maxijra-edu/MUA_UnidadDeteccion/Placa_DetectorParticulas/Componentes/MCP4661T_104E_ML/QFN16_4x4MC_MCH.step

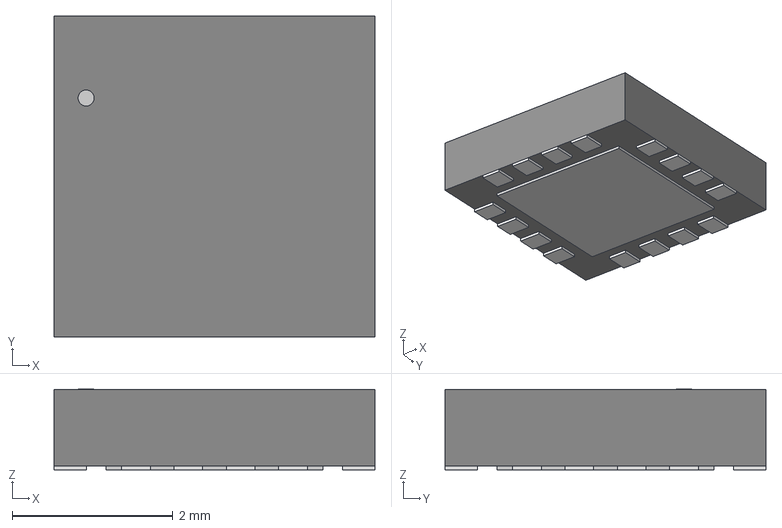
[picture p15: CAD file, 2025-07-07]
Placa_DetectorParticulas/Componentes/MCP4661T_104E_ML/QFN16_4x4MC_MCH.step
3.99 x 3.99 x 1.00 mm
