maxijra-edu/MUA_UnidadDeteccion/Placa_DetectorParticulas/Componentes/MICROFJ-60035-TSV-TR1/MICROFJ-60035-TSV_ONS.step

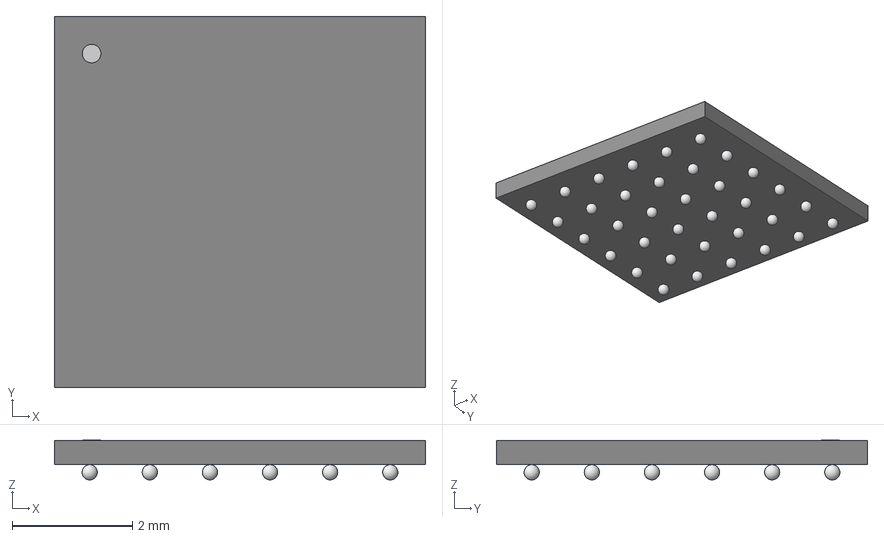
[picture p16: CAD file, 2025-03-27]
Placa_DetectorParticulas/Componentes/MICROFJ-60035-TSV-TR1/MICROFJ-60035-TSV_ONS.step
6.17 x 6.17 x 0.663 mm
