maxijra-edu/MUA_UnidadDeteccion/Placa_DetectorParticulas/Componentes/NXB0108BQ-Q100X/DHVQFN20_SOT764-1_NEX.step

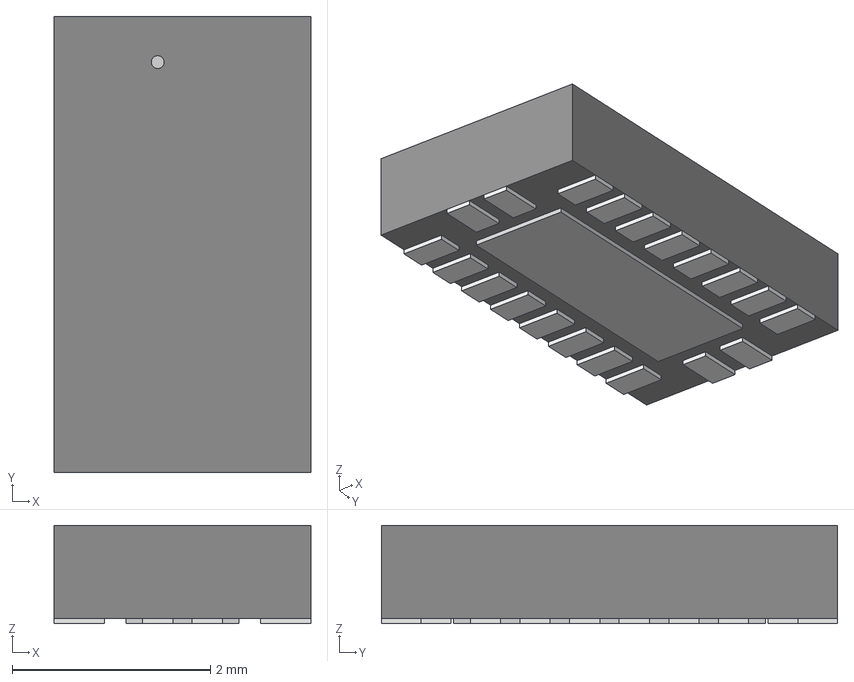
[picture p17: CAD file, 2025-03-27]
Placa_DetectorParticulas/Componentes/NXB0108BQ-Q100X/DHVQFN20_SOT764-1_NEX.step
2.59 x 4.60 x 0.993 mm
