maxijra-edu/MUA_UnidadDeteccion/Placa_DetectorParticulas/Componentes/OPA855QDSGRQ1/DSG0008A.stp

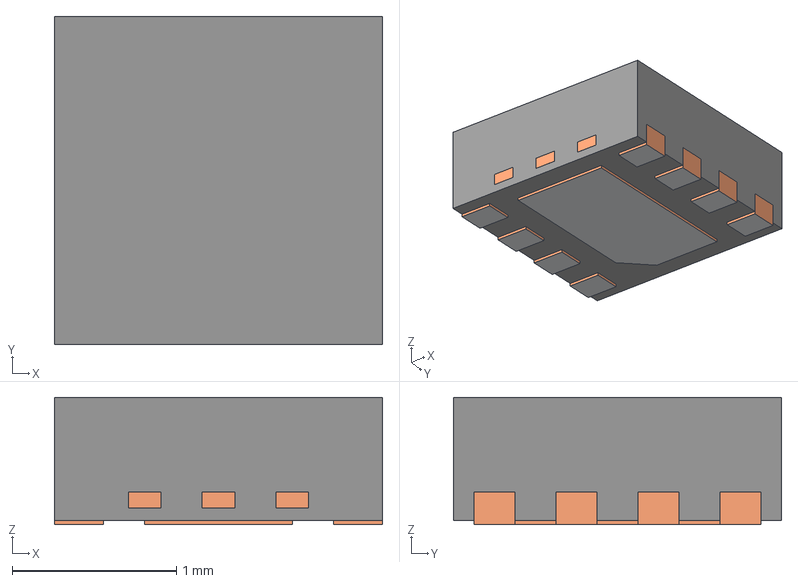
[picture p18: CAD file, 2025-03-27]
Placa_DetectorParticulas/Componentes/OPA855QDSGRQ1/DSG0008A.stp
2.00 x 2.00 x 0.775 mm
BODY-SON
FRAME-DSG0008A
PIN1-ID
