maxijra-edu/MUA_UnidadDeteccion/Placa_DetectorParticulas/Componentes/PCA9306IDCURQ1/DCU0008A.stp

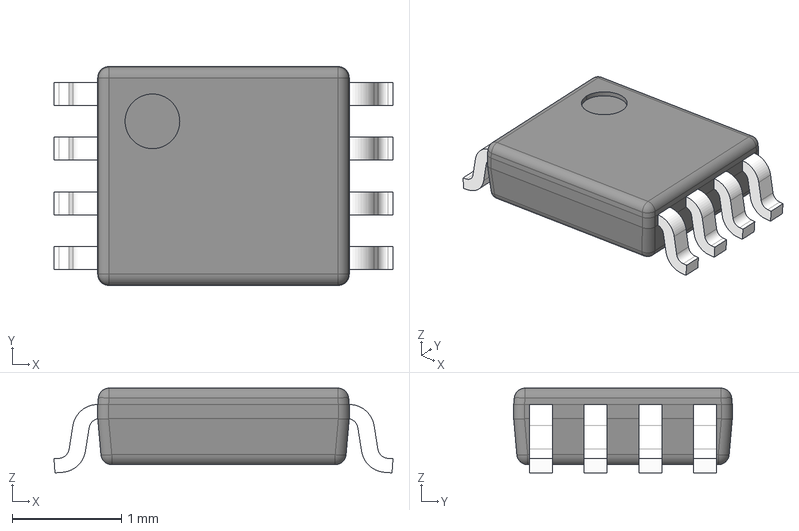
[picture p19: CAD file, 2025-03-27]
Placa_DetectorParticulas/Componentes/PCA9306IDCURQ1/DCU0008A.stp
3.10 x 2.00 x 0.775 mm
BODY-VSSOP
LEAD-VSSOP x 8
