maxijra-edu/MUA_UnidadDeteccion/Placa_DetectorParticulas/Componentes/PMEG4005CEJX/SOD523_NEX.step

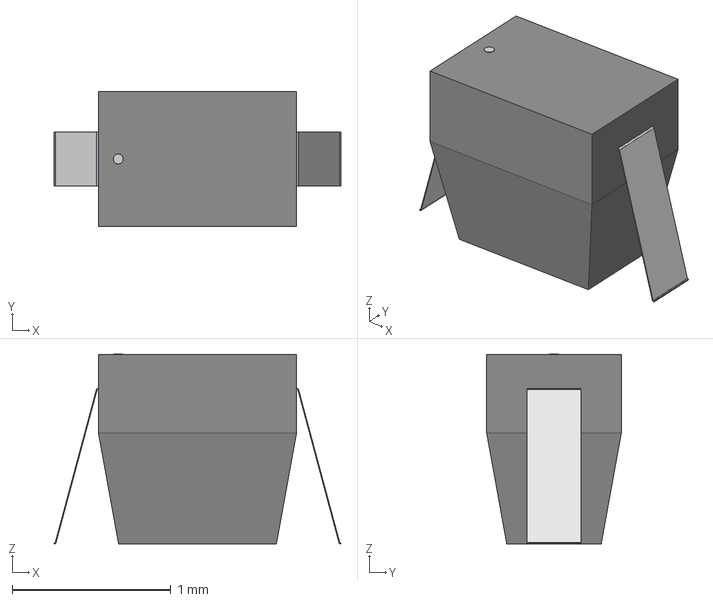
[picture p20: CAD file, 2025-03-27]
Placa_DetectorParticulas/Componentes/PMEG4005CEJX/SOD523_NEX.step
1.81 x 0.85 x 1.20 mm
