maxijra-edu/MUA_UnidadDeteccion/Placa_DetectorParticulas/Componentes/SN74LV1T04QDCKRQ1/SC70-5_DCK_TEX.step

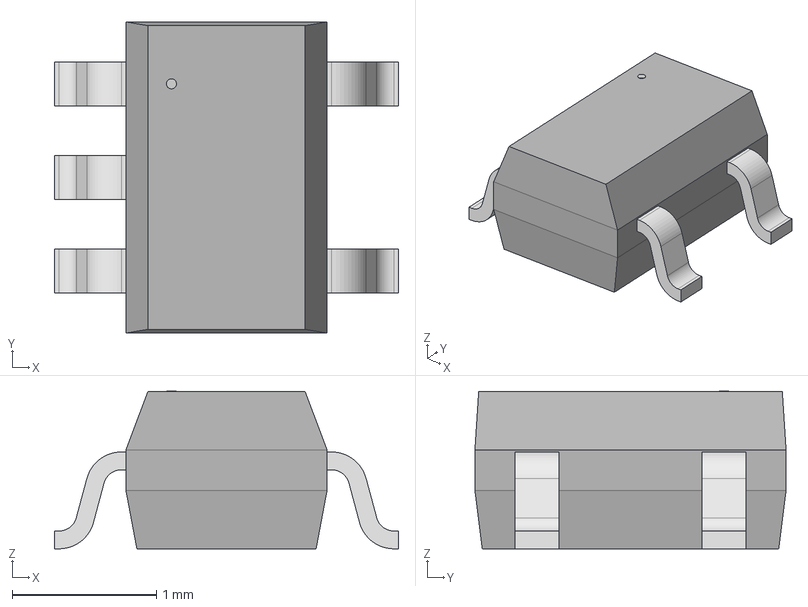
[picture p21: CAD file, 2025-03-27]
Placa_DetectorParticulas/Componentes/SN74LV1T04QDCKRQ1/SC70-5_DCK_TEX.step
2.39 x 2.16 x 1.09 mm
