maxijra-edu/MUA_UnidadDeteccion/Placa_DetectorParticulas/Componentes/TMP100AQDBVRQ1/DBV0006A.stp

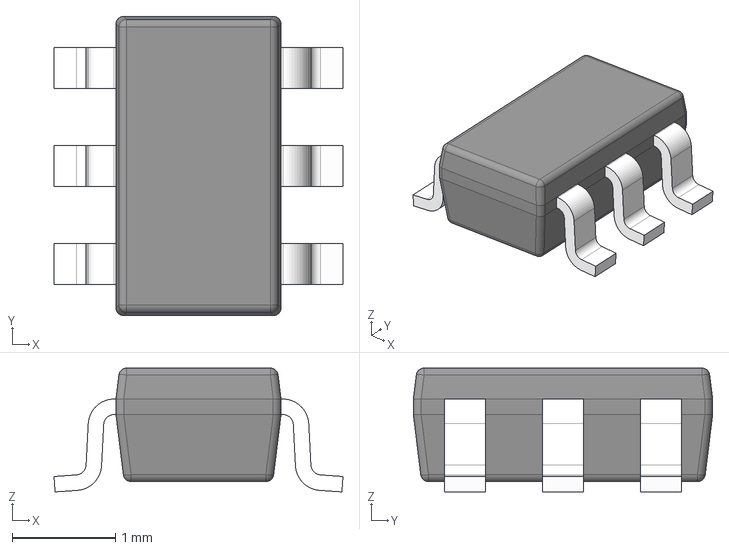
[picture p22: CAD file, 2025-03-27]
Placa_DetectorParticulas/Componentes/TMP100AQDBVRQ1/DBV0006A.stp
2.80 x 2.90 x 1.20 mm
BODY-SOT
LEAD-SOT x 6
