maxijra-edu/MUA_UnidadDeteccion/Placa_DetectorParticulas/Componentes/TS3011IYQ3T/DFN8_2P06X2P06X0P5_STM.step

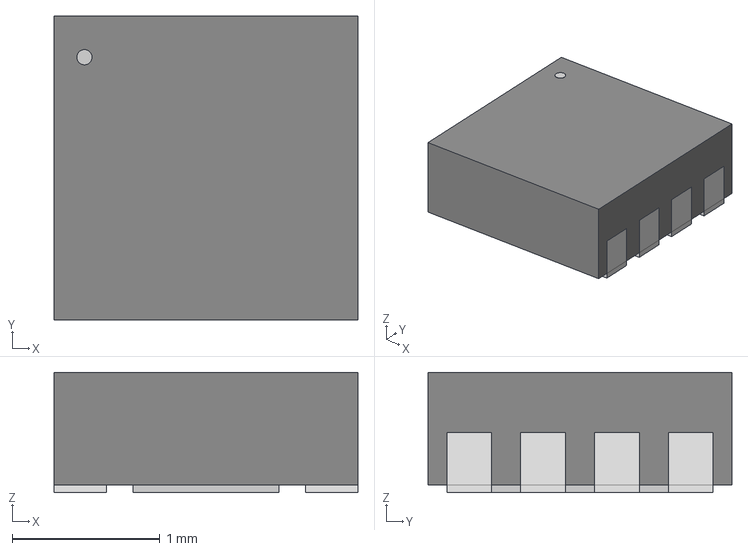
[picture p23: CAD file, 2025-03-27]
Placa_DetectorParticulas/Componentes/TS3011IYQ3T/DFN8_2P06X2P06X0P5_STM.step
2.06 x 2.06 x 0.815 mm
