maxijra-edu/MUA_UnidadDeteccion/Placa_DetectorParticulas/Componentes/TSZ122IQ2T/DFN8_2X2_NB_STM.step

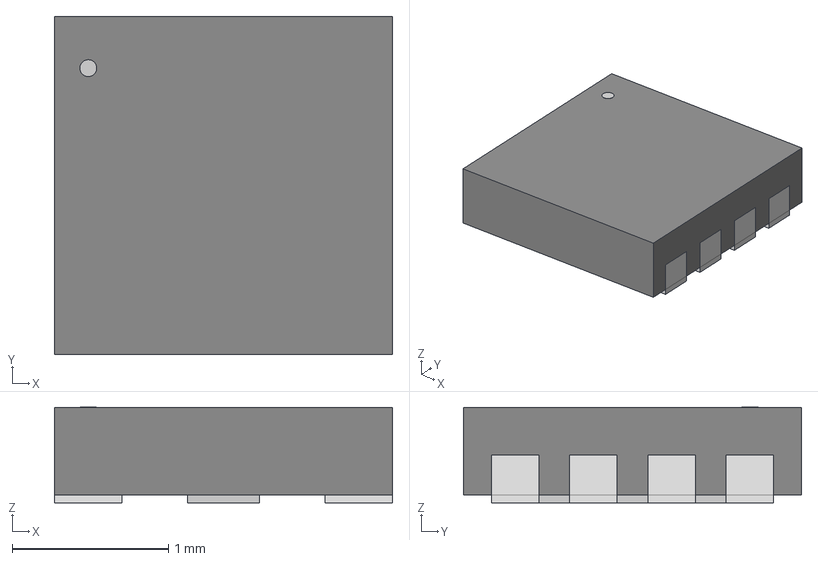
[picture p24: CAD file, 2025-03-27]
Placa_DetectorParticulas/Componentes/TSZ122IQ2T/DFN8_2X2_NB_STM.step
2.16 x 2.16 x 0.612 mm
