maxijra-edu/MUA_UnidadDeteccion/Placa_DetectorParticulas/Componentes/TSZ122IYST/MINISO8_TSZ122_STM.step

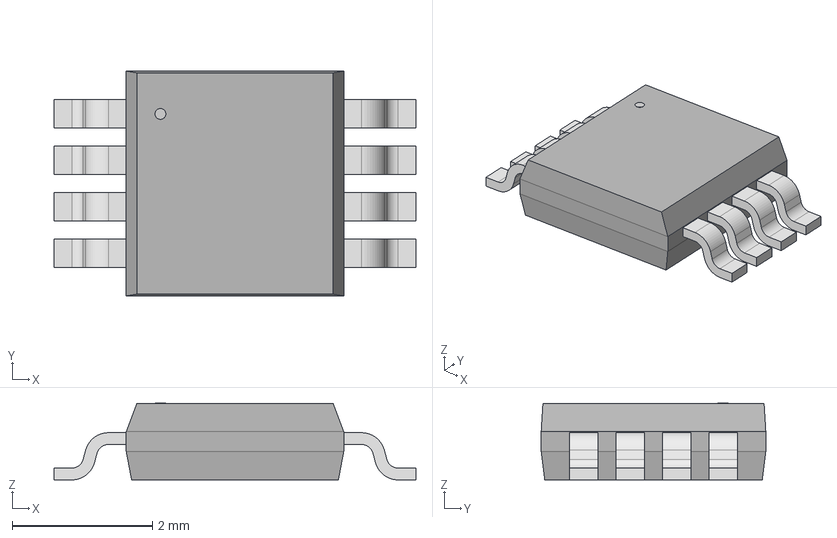
[picture p25: CAD file, 2025-03-27]
Placa_DetectorParticulas/Componentes/TSZ122IYST/MINISO8_TSZ122_STM.step
5.16 x 3.20 x 1.09 mm
