maxijra-edu/MUA_UnidadDeteccion/Placa_DetectorParticulas/Modelo3D-Placa_DetectorParticulas.step

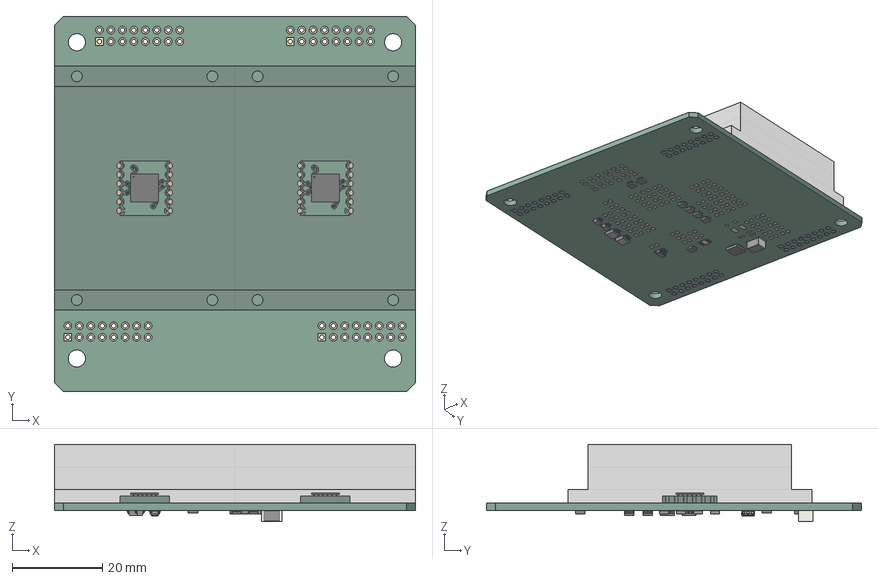
[picture p26: CAD file, 2025-03-27]
Placa_DetectorParticulas/Modelo3D-Placa_DetectorParticulas.step
80.0 x 83.0 x 17.1 mm
Local_CS_d980
Pcb_d980
PCB_Sketch_d980
topPads_d980
botPads_d980
Cuerpo x 2
Cuerpo002 x 2
Pcb_1cf2 x 2
topPads_1cf2_cut x 2
topPads_1cf2_cut001 x 2
topPads_1cf2_cut002 x 2
topPads_1cf2_cut003 x 2
topPads_1cf2_cut004 x 2
topPads_1cf2_cut005 x 2
topPads_1cf2_cut006 x 2
topPads_1cf2_cut007 x 2
topPads_1cf2_cut008 x 2
topPads_1cf2_cut009 x 2
topPads_1cf2_cut010 x 2
topPads_1cf2_cut011 x 2
topPads_1cf2_cut012 x 2
topPads_1cf2_cut013 x 2
topPads_1cf2_cut014 x 2
topPads_1cf2_cut015 x 2
topPads_1cf2_cut016 x 2
topPads_1cf2_cut017 x 2
topPads_1cf2_cut018 x 2
topPads_1cf2_cut019 x 2
topPads_1cf2_cut020 x 2
topPads_1cf2_cut021 x 2
topPads_1cf2_cut022 x 2
topPads_1cf2_cut023 x 2
topPads_1cf2_cut024 x 2
topPads_1cf2_cut025 x 2
topPads_1cf2_cut026 x 2
topPads_1cf2_cut027 x 2
topPads_1cf2_cut028 x 2
topPads_1cf2_cut029 x 2
topPads_1cf2_cut030 x 2
topPads_1cf2_cut031 x 2
topPads_1cf2_cut032 x 2
topPads_1cf2_cut033 x 2
topPads_1cf2_cut034 x 2
topPads_1cf2_cut035 x 2
topPads_1cf2_cut036 x 2
topPads_1cf2_cut037 x 2
topPads_1cf2_cut038 x 2
topPads_1cf2_cut039 x 2
topPads_1cf2_cut040 x 2
topPads_1cf2_cut041 x 2
topPads_1cf2_cut042 x 2
topPads_1cf2_cut043 x 2
topPads_1cf2_cut044 x 2
topPads_1cf2_cut045 x 2
topPads_1cf2_cut046 x 2
topPads_1cf2_cut047 x 2
topPads_1cf2_cut048 x 2
topPads_1cf2_cut049 x 2
topPads_1cf2_cut050 x 2
topPads_1cf2_cut051 x 2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
