maxijra-edu/MUA_UnidadDeteccion/Placa_SiPM/Placa_SiPM_union.FCStd

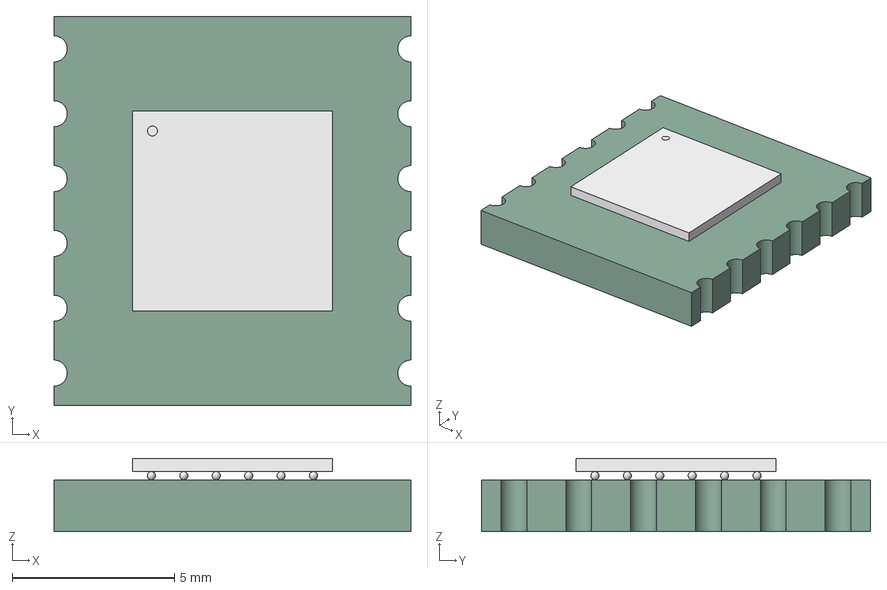
[picture p27: CAD file, 2025-03-27]
Placa_SiPM/Placa_SiPM_union.FCStd
11.0 x 12.0 x 2.26 mm
Pcb_1cf2
