maxijra-edu/MUA_UnidadDeteccion/Placa_DetectorParticulas/Componentes/74LVC2G00DP-Q100H/TSSOP8_SOT505-2_NEX.step

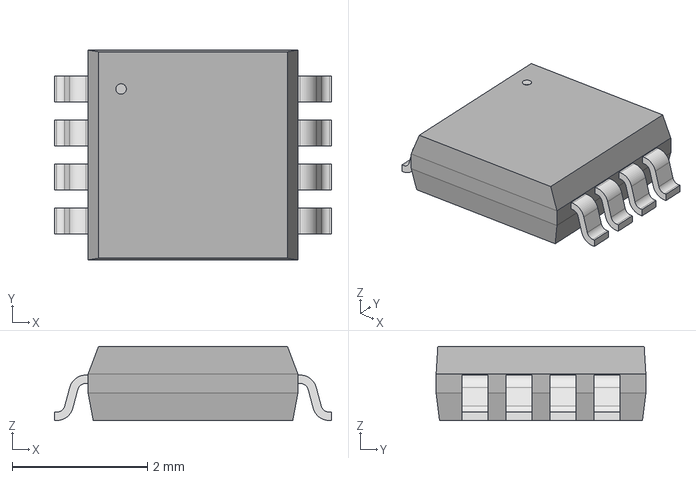
[picture p28: CAD file, 2025-03-27]
Placa_DetectorParticulas/Componentes/74LVC2G00DP-Q100H/TSSOP8_SOT505-2_NEX.step
4.09 x 3.10 x 1.09 mm
