maxijra-edu/MUA_UnidadDeteccion/Placa_DetectorParticulas/Componentes/Centellador/CentelladorV2.FCStd

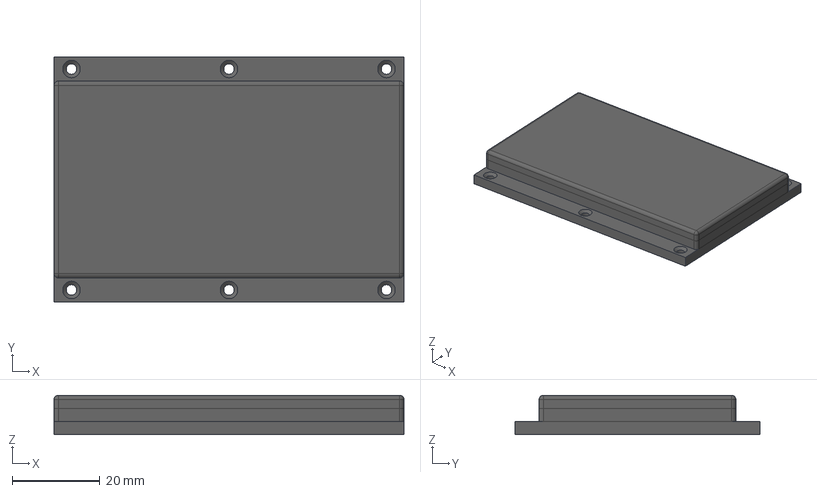
[picture p29: CAD file, 2025-03-27]
Placa_DetectorParticulas/Componentes/Centellador/CentelladorV2.FCStd
80.0 x 56.0 x 9.00 mm
Centellador_2
Cuerpo
Centellador_1
