maxijra-edu/MUA_UnidadDeteccion/Placa_DetectorParticulas/Componentes/SiPM_Board/Placa_SiPM.FCStd

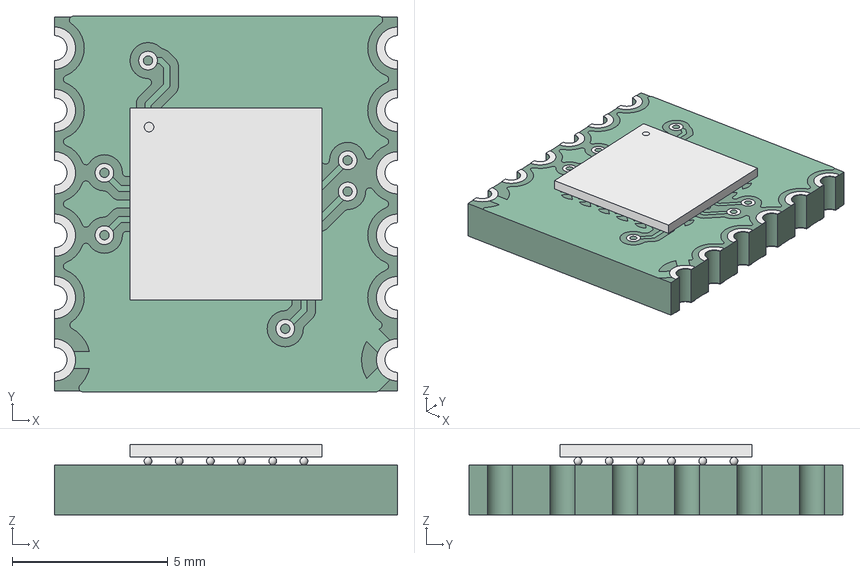
[picture p31: CAD file, 2025-03-27]
Placa_DetectorParticulas/Componentes/SiPM_Board/Placa_SiPM.FCStd
11.0 x 12.0 x 2.28 mm
Pcb_1cf2
topPads_1cf2_cut
topTracks_1cf2
topZones_1cf2
botPads_1cf2_cut
botTracks_1cf2
