maxijra-edu/MUA_UnidadDeteccion/Modelos_3D/CarcasaV3Threaded.step

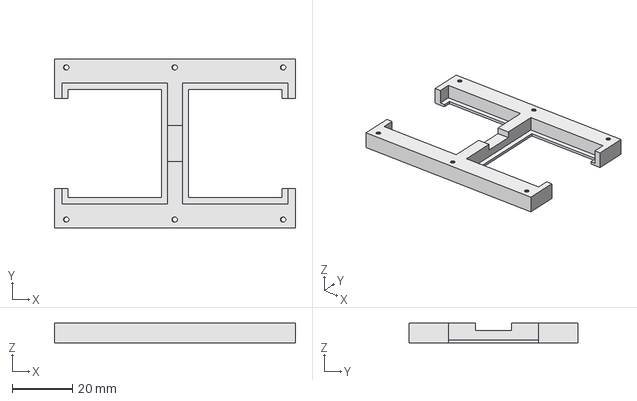
[picture p32: CAD file, 2025-07-07]
Modelos_3D/CarcasaV3Threaded.step
80.0 x 56.0 x 6.50 mm
