maxijra-edu/MUA_UnidadDeteccion/Placa_DetectorParticulas/Componentes/Centellador/Centellador.FCStd

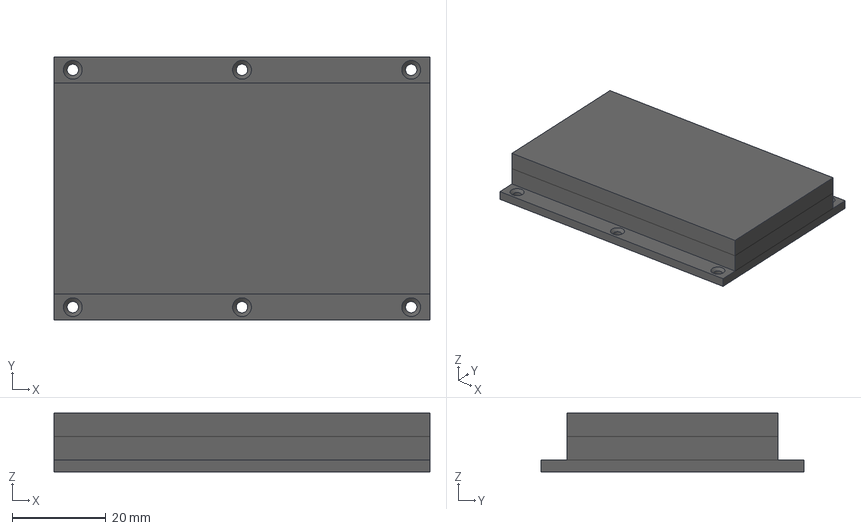
[picture p33: CAD file, 2025-03-27]
Placa_DetectorParticulas/Componentes/Centellador/Centellador.FCStd
80.0 x 56.0 x 12.5 mm
Centellador_2
Cuerpo
Centellador_1
