maxijra-edu/MUA_UnidadDeteccion/Modelos_3D/CarcasaV3.step

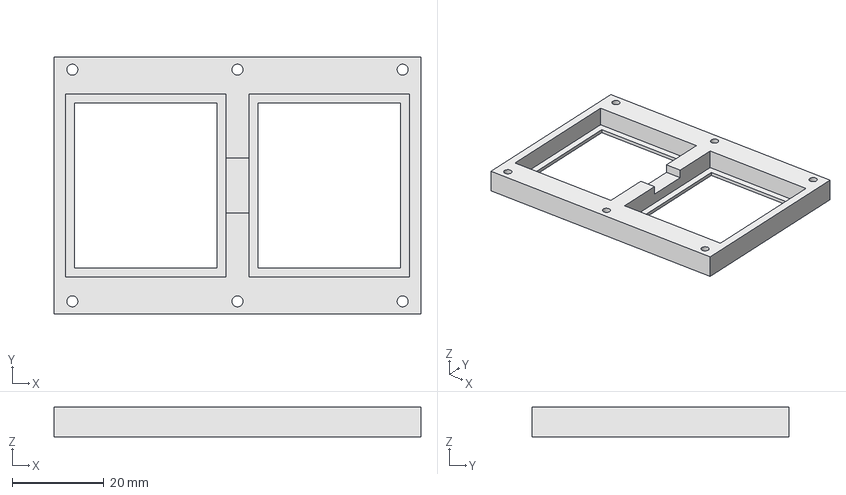
[picture p34: CAD file, 2025-03-27]
Modelos_3D/CarcasaV3.step
80.0 x 56.0 x 6.50 mm
