maxijra-edu/MUA_UnidadDeteccion/Placa_DetectorParticulas/Componentes/Centellador/Pata.FCStd

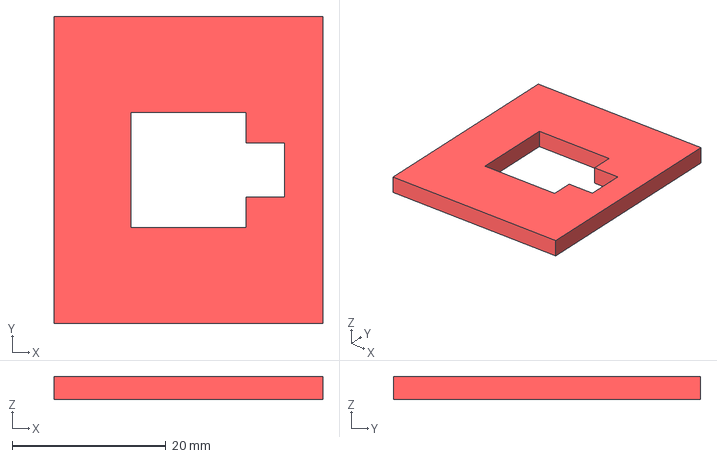
[picture p36: CAD file, 2025-03-27]
Placa_DetectorParticulas/Componentes/Centellador/Pata.FCStd
35.0 x 40.0 x 3.00 mm
