maxijra-edu/MUA_UnidadDeteccion/Modelos_3D/PlacaCarcasaV3.FCStd

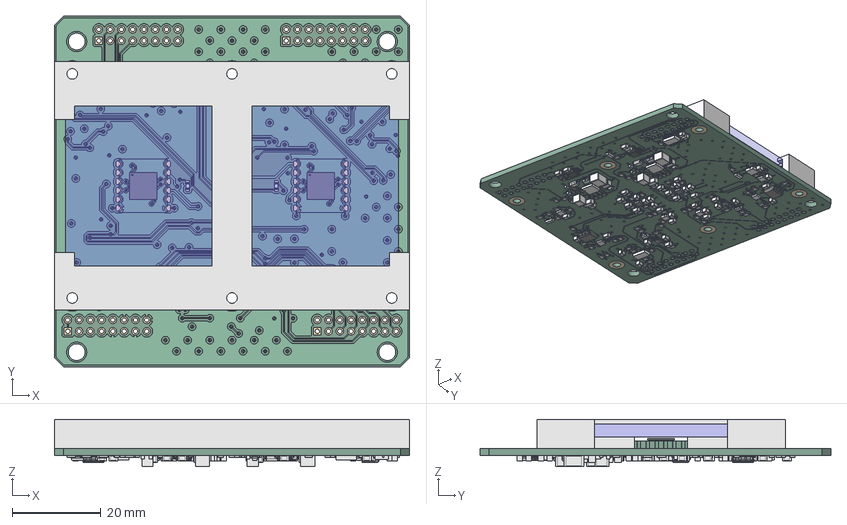
[picture p37: CAD file, 2025-03-27]
Modelos_3D/PlacaCarcasaV3.FCStd
80.0 x 79.0 x 10.6 mm
Pcb_d980
topPads_d980
topTracks_d980
topZones_d980
botPads_d980
botTracks_d980
botZones_d980
BODY-SOT
LEAD-SOT
LEAD-SOT001
LEAD-SOT002
LEAD-SOT003
LEAD-SOT004
LEAD-SOT005
06_PlacasSiPM.kicad_sch_LED_0603_1608Metric_667c60cf1737 x 2
07_SensorTemperatura.kicad_sch_C_0805_2012Metric_4f3bec8a4ad3 x 46
Cuerpo
Pcb_1cf2 x 2
topPads_1cf2_cut x 2
topPads_1cf2_cut001 x 2
topPads_1cf2_cut002 x 2
topPads_1cf2_cut003 x 2
topPads_1cf2_cut004 x 2
topPads_1cf2_cut005 x 2
topPads_1cf2_cut006 x 2
topPads_1cf2_cut007 x 2
topPads_1cf2_cut008 x 2
topPads_1cf2_cut009 x 2
topPads_1cf2_cut010 x 2
topPads_1cf2_cut011 x 2
topPads_1cf2_cut012 x 2
topPads_1cf2_cut013 x 2
topPads_1cf2_cut014 x 2
topPads_1cf2_cut015 x 2
topPads_1cf2_cut016 x 2
topPads_1cf2_cut017 x 2
topPads_1cf2_cut018 x 2
topPads_1cf2_cut019 x 2
topPads_1cf2_cut020 x 2
topPads_1cf2_cut021 x 2
topPads_1cf2_cut022 x 2
topPads_1cf2_cut023 x 2
topPads_1cf2_cut024 x 2
topPads_1cf2_cut025 x 2
topPads_1cf2_cut026 x 2
topPads_1cf2_cut027 x 2
topPads_1cf2_cut028 x 2
topPads_1cf2_cut029 x 2
topPads_1cf2_cut030 x 2
topPads_1cf2_cut031 x 2
topPads_1cf2_cut032 x 2
topPads_1cf2_cut033 x 2
topPads_1cf2_cut034 x 2
topPads_1cf2_cut035 x 2
topPads_1cf2_cut036 x 2
topPads_1cf2_cut037 x 2
topPads_1cf2_cut038 x 2
topPads_1cf2_cut039 x 2
topPads_1cf2_cut040 x 2
topPads_1cf2_cut041 x 2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
