maxijra-edu/MUA_UnidadDeteccion/Placa_DetectorParticulas/Componentes/Centellador/CarcasaV3.step

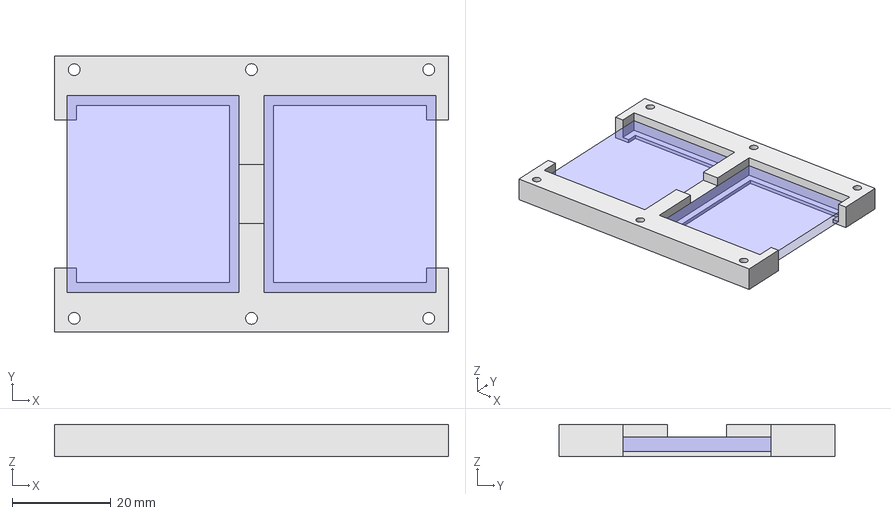
[picture p38: CAD file, 2025-03-27]
Placa_DetectorParticulas/Componentes/Centellador/CarcasaV3.step
80.0 x 56.0 x 6.50 mm
Cuerpo
